aitesam961/Red-Crab/References/Screenshot 2022-07-08 204516.png

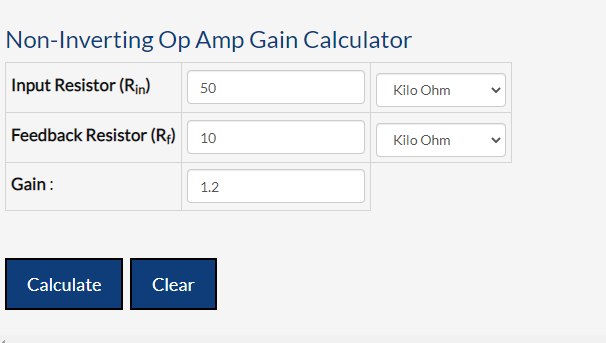
References/Screenshot 2022-07-08 204516.png
